Zain-Ul-Islam-Siddiqui/Carrier-Board/Deliverables/Renderings/2D_Bottom_View.PNG

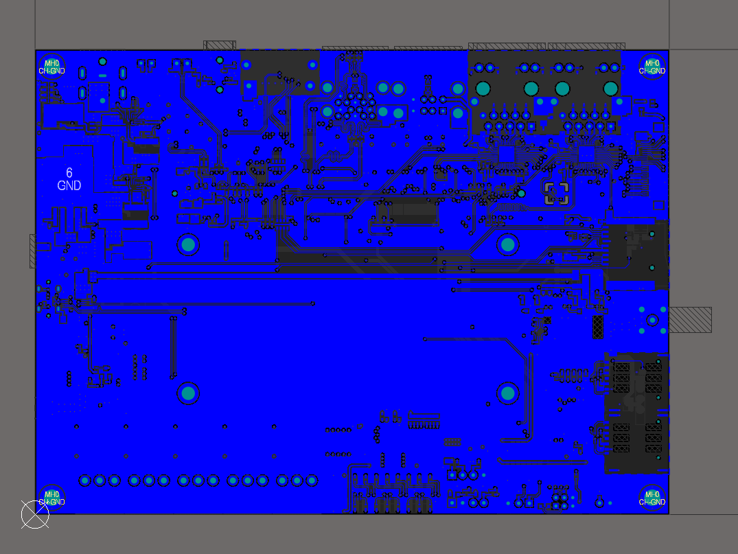
Deliverables/Renderings/2D_Bottom_View.PNG
