Zain-Ul-Islam-Siddiqui/Carrier-Board/Deliverables/Renderings/2D_C_View.png

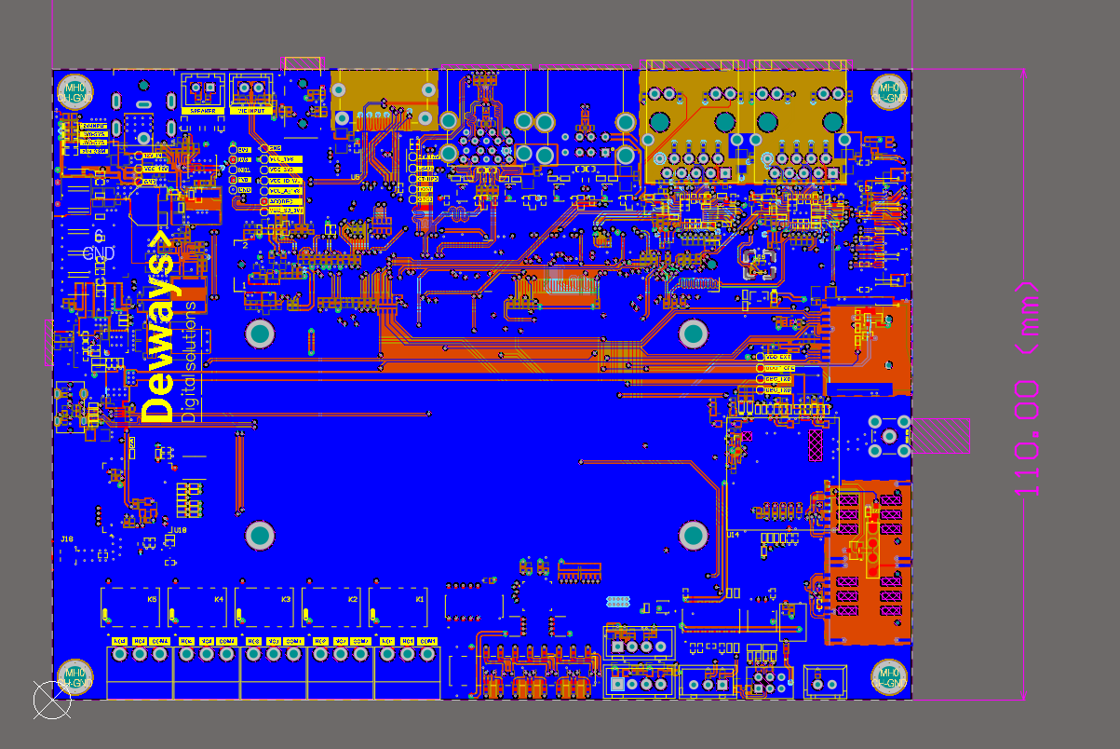
Deliverables/Renderings/2D_C_View.png
