Zain-Ul-Islam-Siddiqui/Carrier-Board/Deliverables/Renderings/2D_L6_View.png

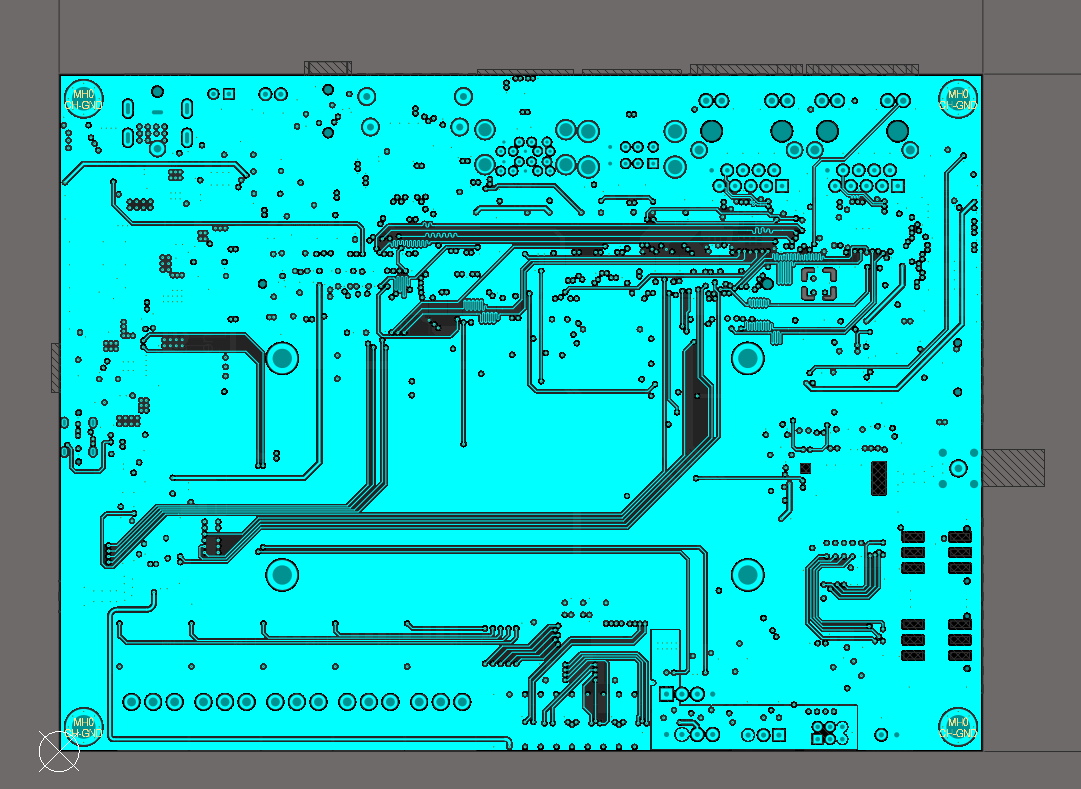
Deliverables/Renderings/2D_L6_View.png
