Zain-Ul-Islam-Siddiqui/Carrier-Board/Deliverables/Renderings/2D_L7View.png

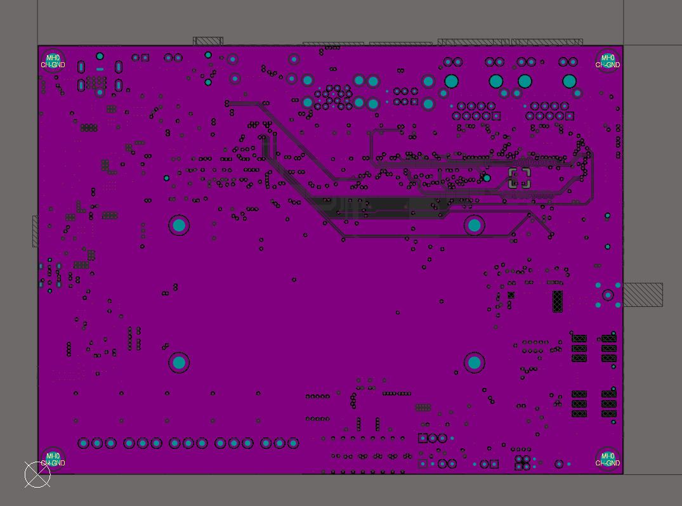
Deliverables/Renderings/2D_L7View.png
