Zain-Ul-Islam-Siddiqui/Carrier-Board/Deliverables/Renderings/Isometric_View.PNG

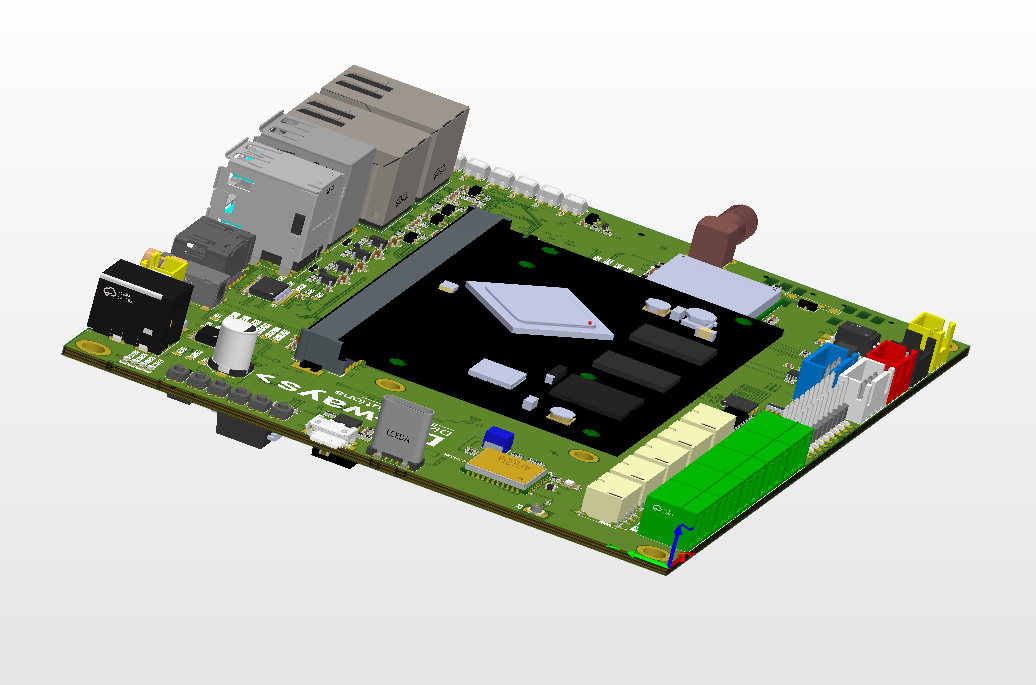
Deliverables/Renderings/Isometric_View.PNG
